MohamedKhay154/stm32-sim808-gps-mqtt/Images/Node-Red/Flow Node-Red.png

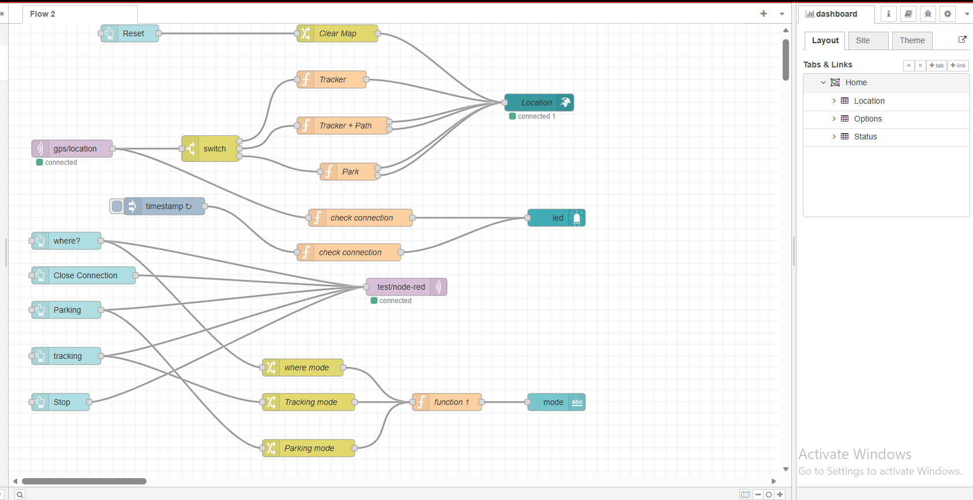
Images/Node-Red/Flow Node-Red.png
