MohamedKhay154/stm32-sim808-gps-mqtt/Images/PCB/3D Bottom SIM808 Board.png

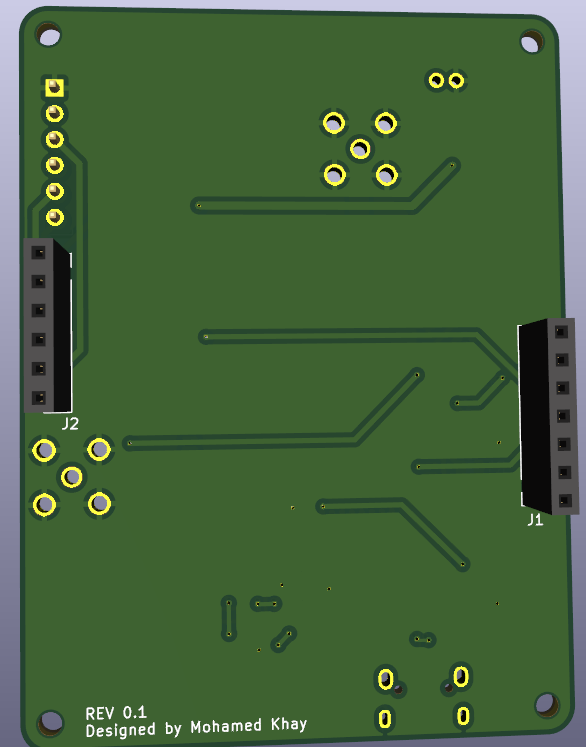
Images/PCB/3D Bottom SIM808 Board.png
