MohamedKhay154/stm32-sim808-gps-mqtt/Images/PCB/First Layer SIM808 Board.png

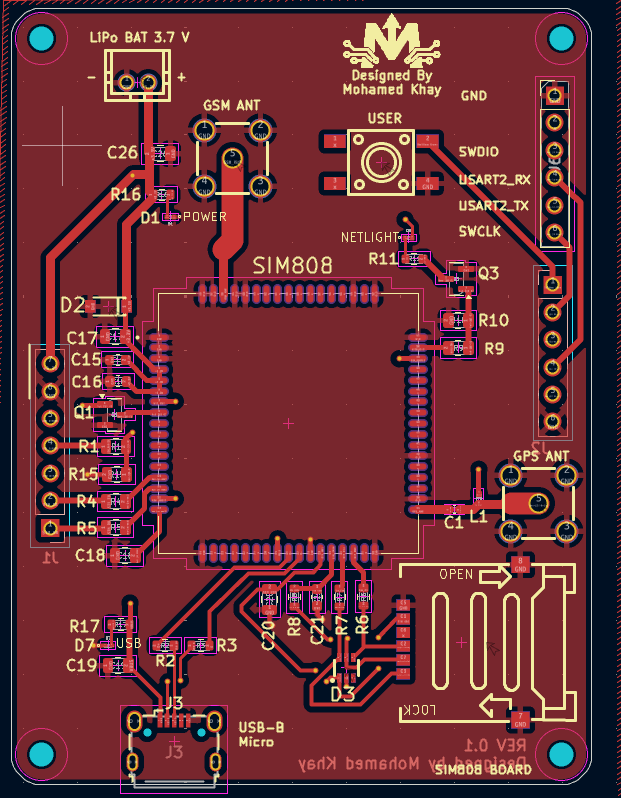
Images/PCB/First Layer SIM808 Board.png
