MohamedKhay154/stm32-sim808-gps-mqtt/Images/PCB/Second Layer STM32 Board.png

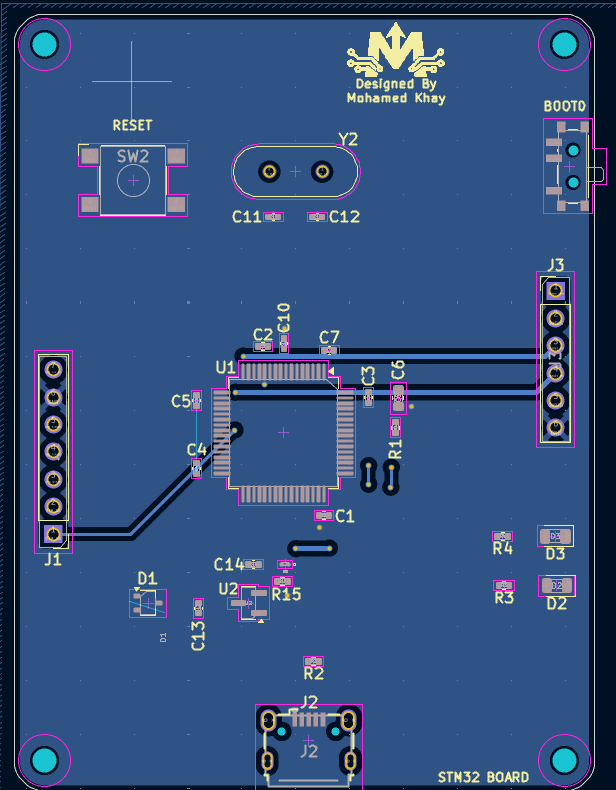
Images/PCB/Second Layer STM32 Board.png
